npsantini/KameraflY-ESP32-CAM-Camera-Swarm-System/misc/Package-Decision.JPG

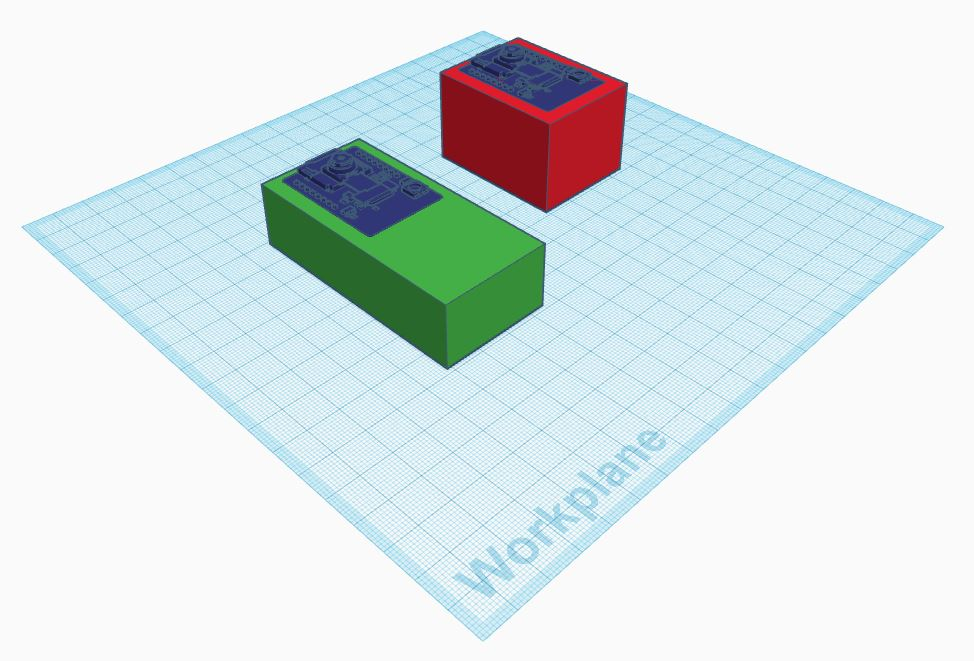
misc/Package-Decision.JPG
