npsantini/KameraflY-ESP32-CAM-Camera-Swarm-System/readme/blynk-3.JPG

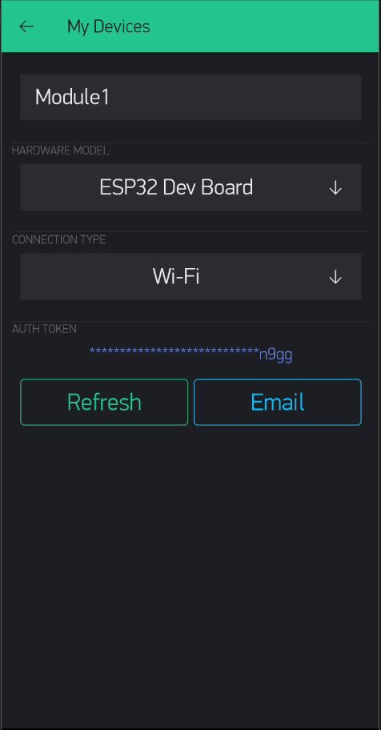
readme/blynk-3.JPG
