npsantini/KameraflY-ESP32-CAM-Camera-Swarm-System/3D-Printing/battery-holder-3.JPG

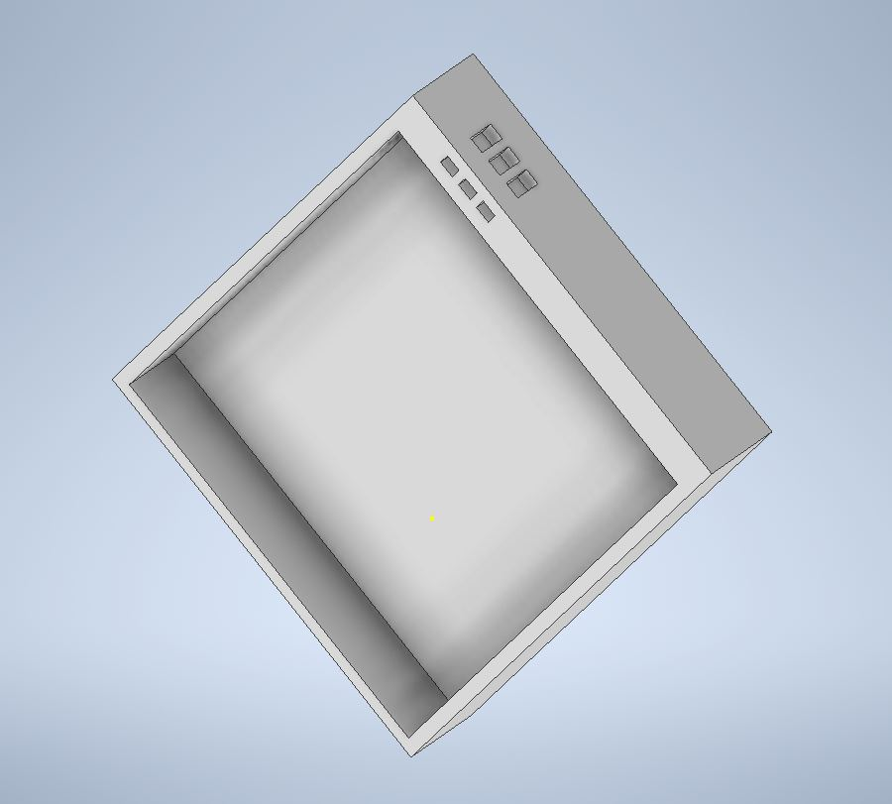
3D-Printing/battery-holder-3.JPG
