npsantini/KameraflY-ESP32-CAM-Camera-Swarm-System/camerafly-firmware-sketch-1.0/src/secrets.h

#define SECRET_SSID "***ssid name here***"
#define SECRET_PASSWORD "***wifi password here***"

#define SECRET_FTP_SERVER "***FTP SERVER IP HERE***"
#define SECRET_FTP_USERNAME "***FTP SERVER USERNAME HERE***" // ie. user@example.com
#define SECRET_FTP_PASSWORD "***FTP PASSWORD HERE***"
